dreamshader/3D_Printing/Images/blender-camera.jpg

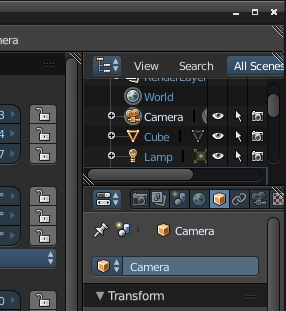
Images/blender-camera.jpg
