dreamshader/3D_Printing/Images/blender-union.jpg

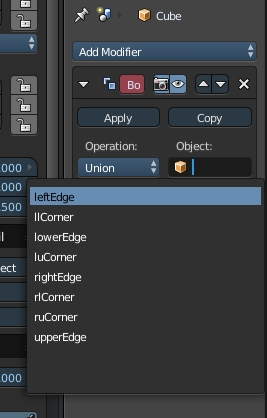
Images/blender-union.jpg
