dreamshader/3D_Printing/Images/cura-anordnung-halter.png

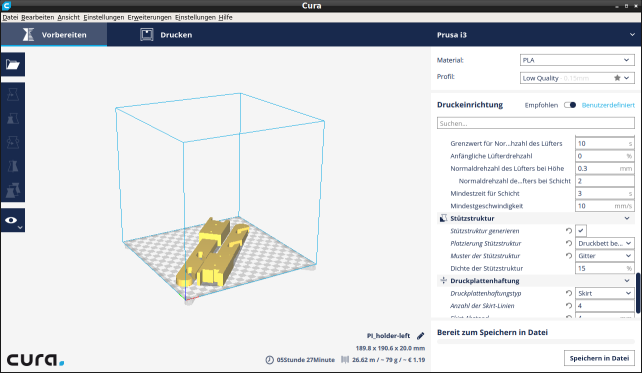
Images/cura-anordnung-halter.png
