dreamshader/3D_Printing/Images/filament-halter-teile.jpg

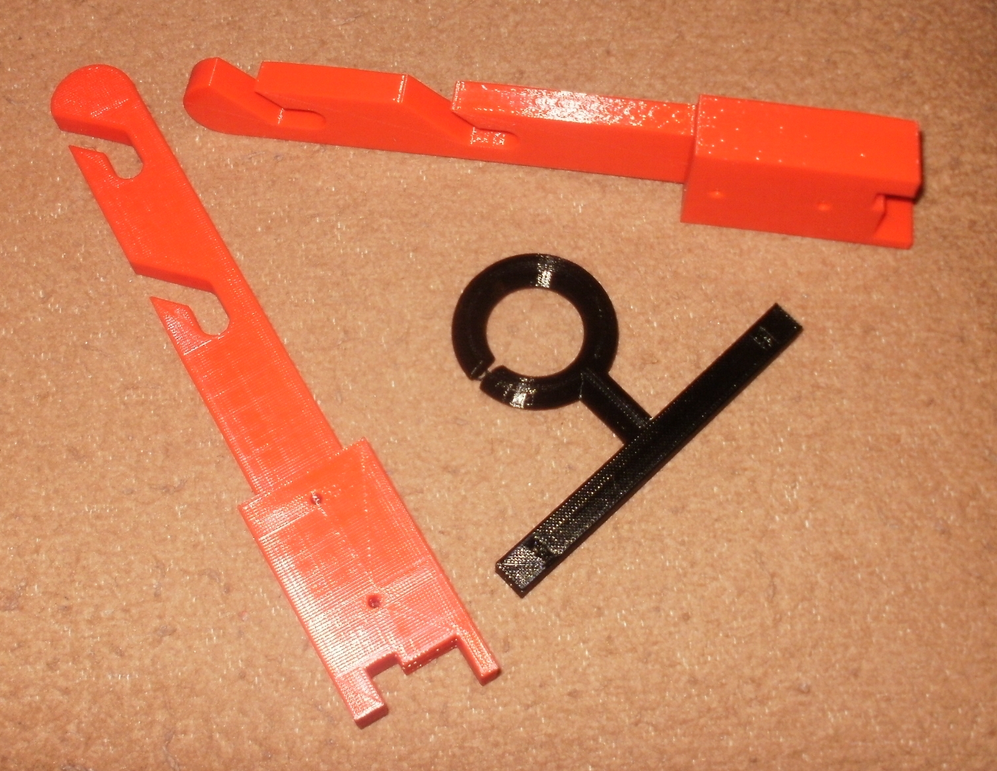
Images/filament-halter-teile.jpg
