dreamshader/3D_Printing/Images/filament-halter.jpg

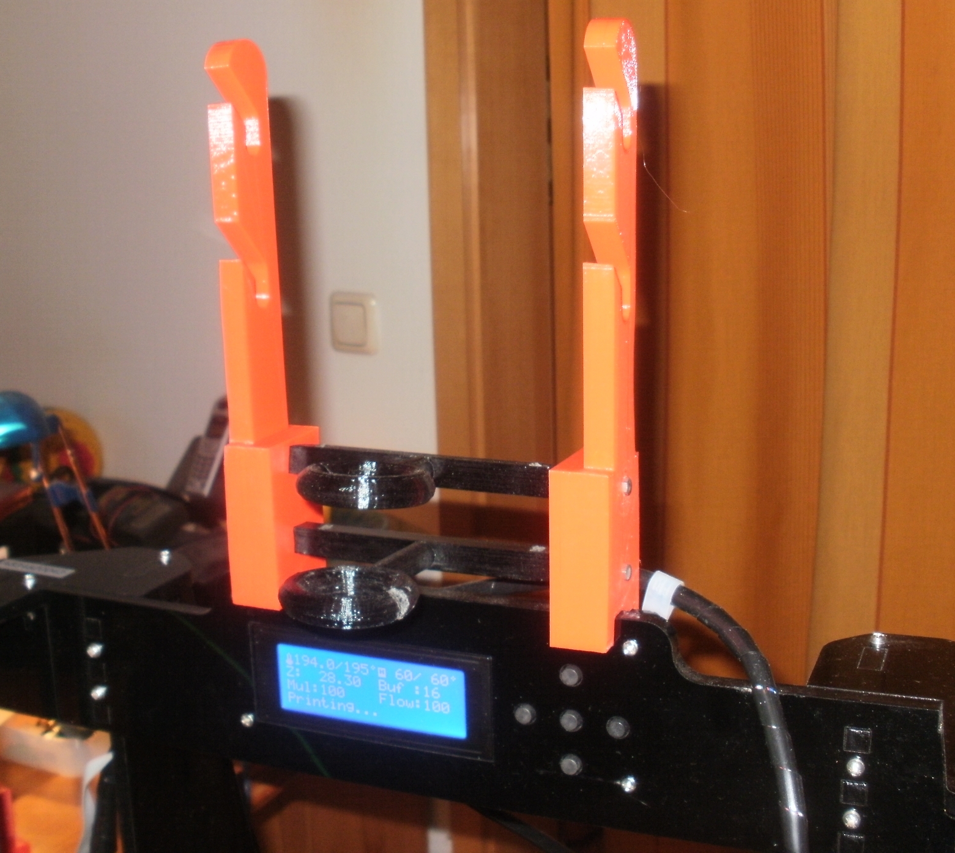
Images/filament-halter.jpg
