dreamshader/3D_Printing/Images/pi-B2-3-board.png

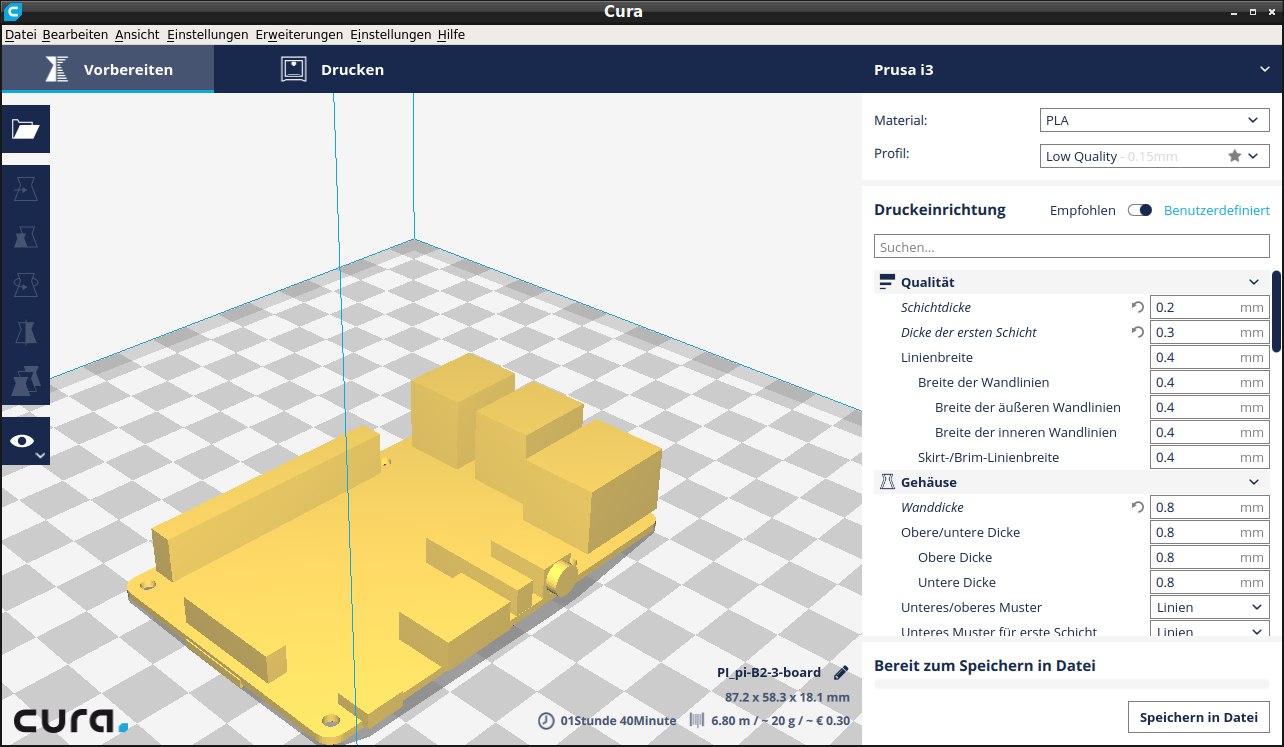
Images/pi-B2-3-board.png
