dreamshader/3D_Printing/Images/pi-bplus_2_3-2.png

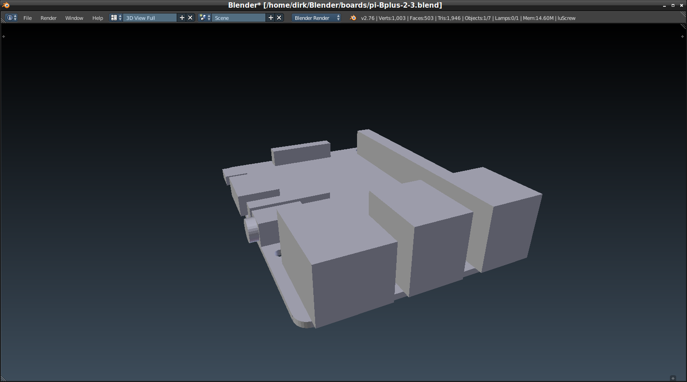
Images/pi-bplus_2_3-2.png
