dreamshader/3D_Printing/Images/pi-zero-board.png

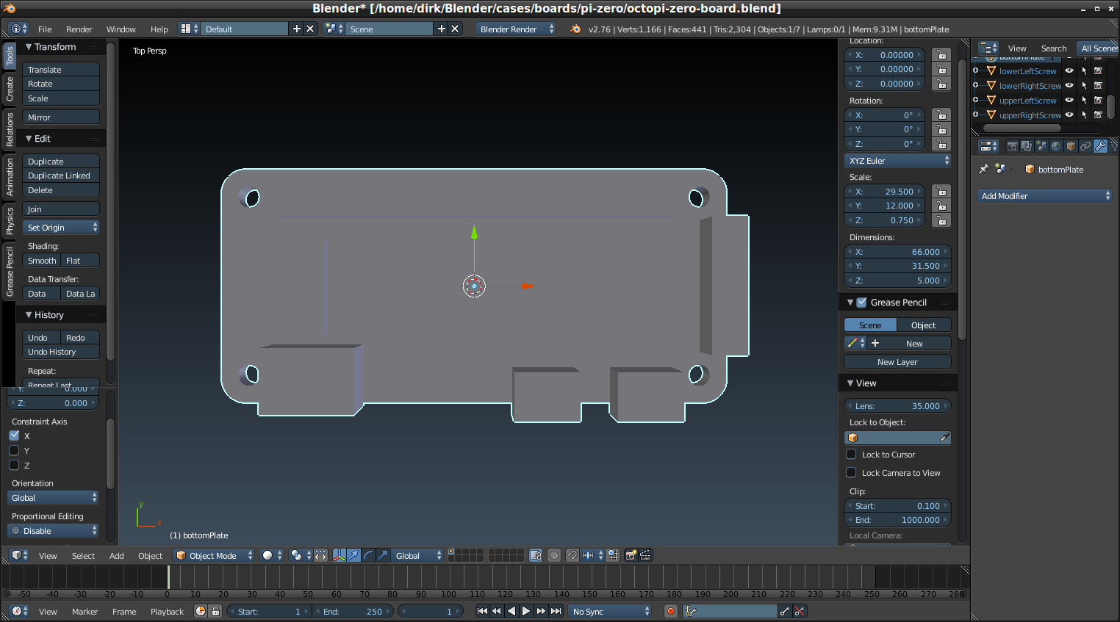
Images/pi-zero-board.png
