dreamshader/3D_Printing/Images/raw/PA100625.JPG

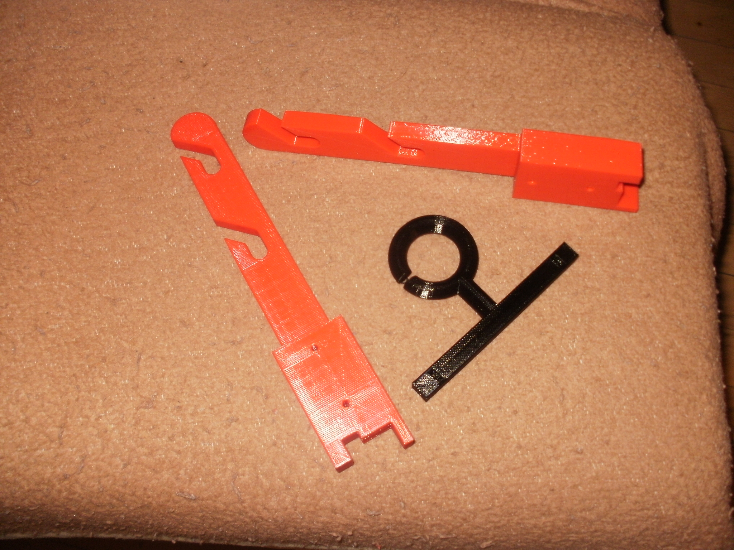
Images/raw/PA100625.JPG
