dreamshader/3D_Printing/Images/raw/PA120630.JPG

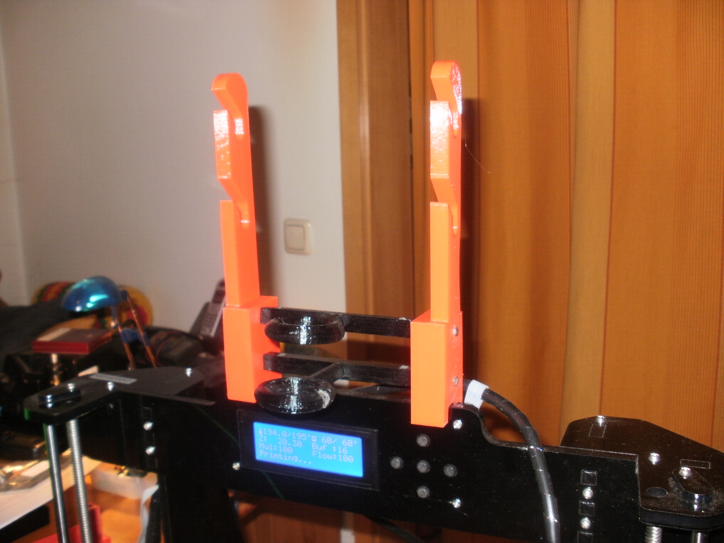
Images/raw/PA120630.JPG
