dreamshader/3D_Printing/Images/raw/PA120635.JPG

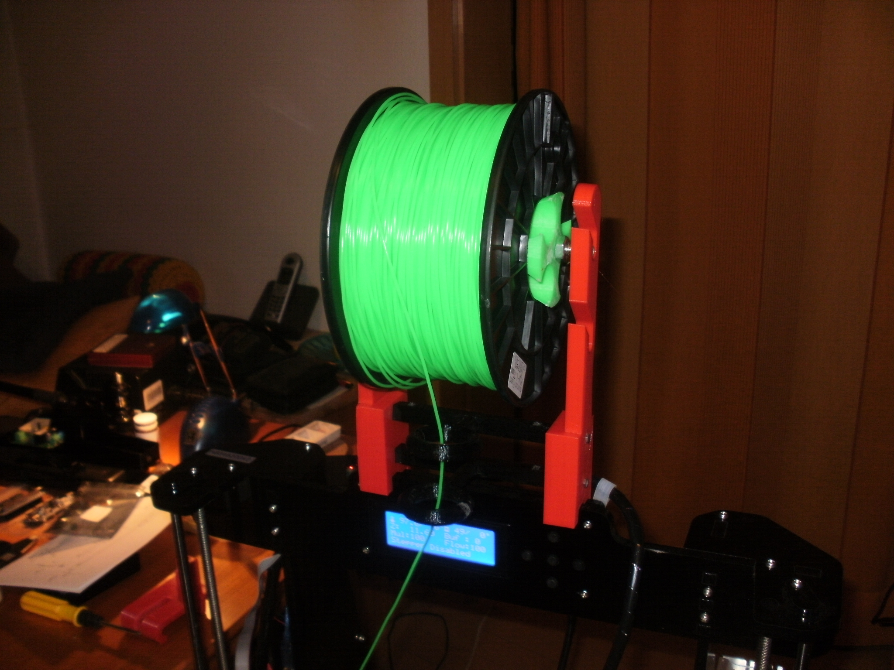
Images/raw/PA120635.JPG
