dreamshader/3D_Printing/Images/raw/PA150643.JPG

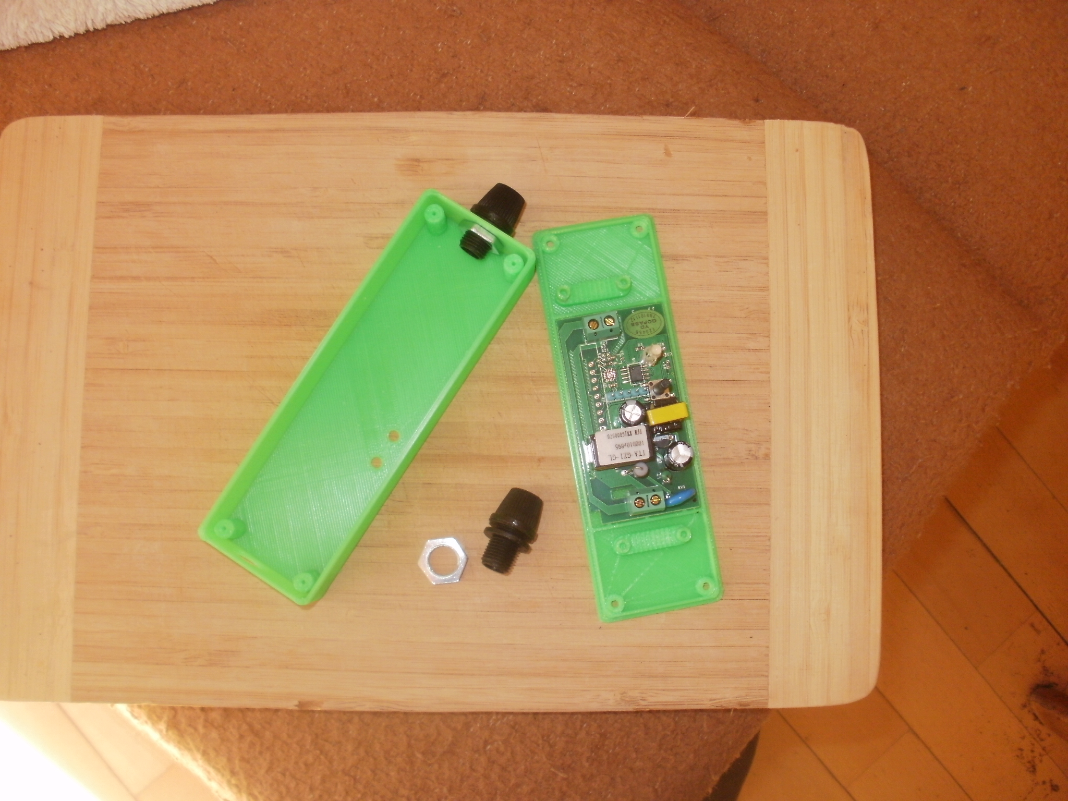
Images/raw/PA150643.JPG
