dreamshader/3D_Printing/Images/raw/PA150644.JPG

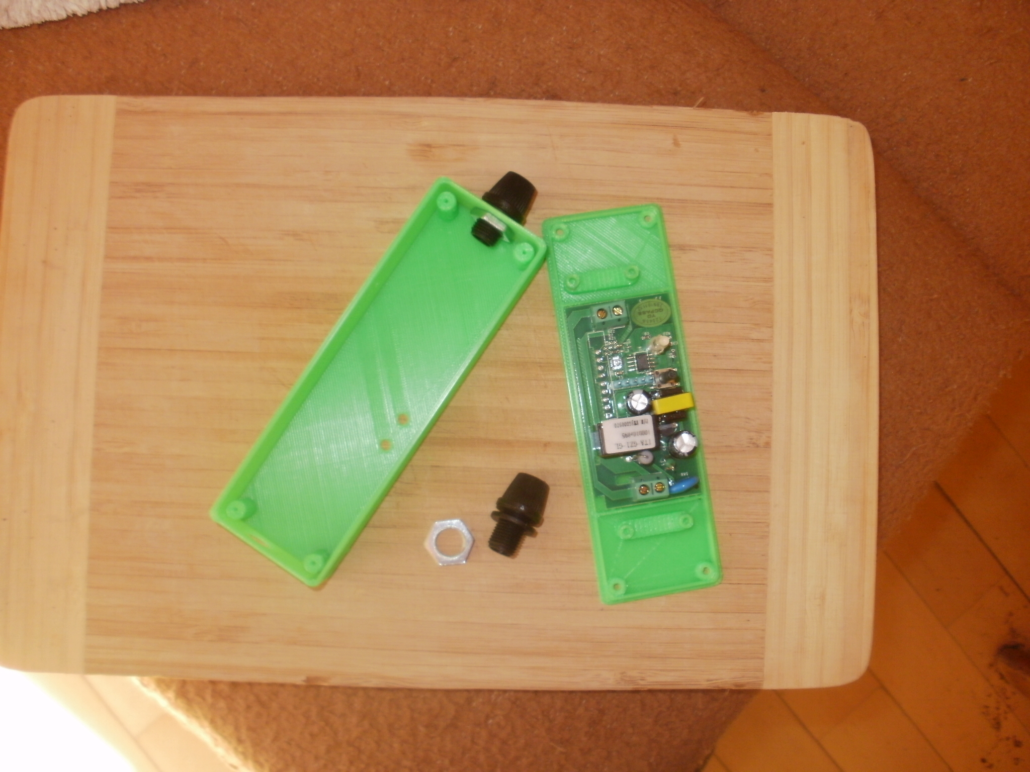
Images/raw/PA150644.JPG
