dreamshader/3D_Printing/Images/raw/PA170645.JPG

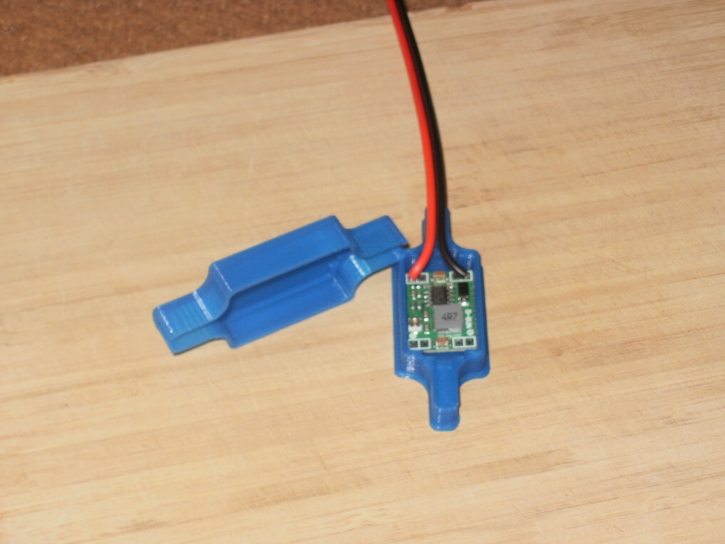
Images/raw/PA170645.JPG
