dreamshader/3D_Printing/Images/raw/PA170646.JPG

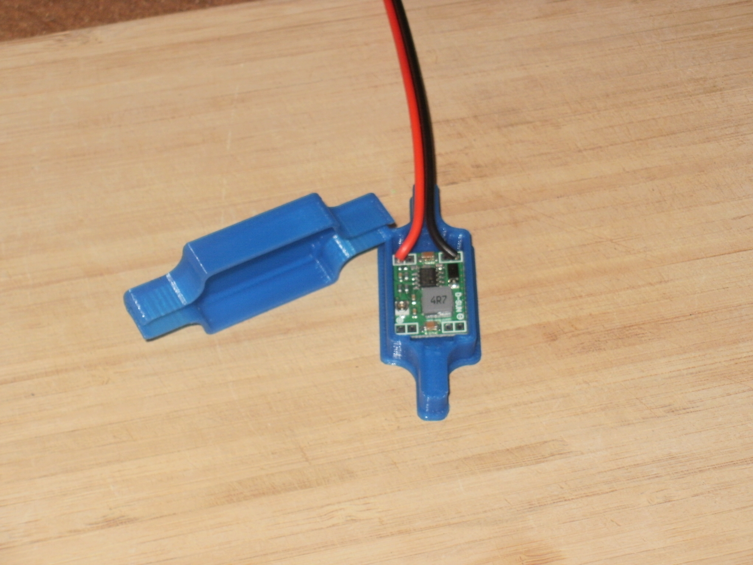
Images/raw/PA170646.JPG
