dreamshader/3D_Printing/Images/raw/PA170647.JPG

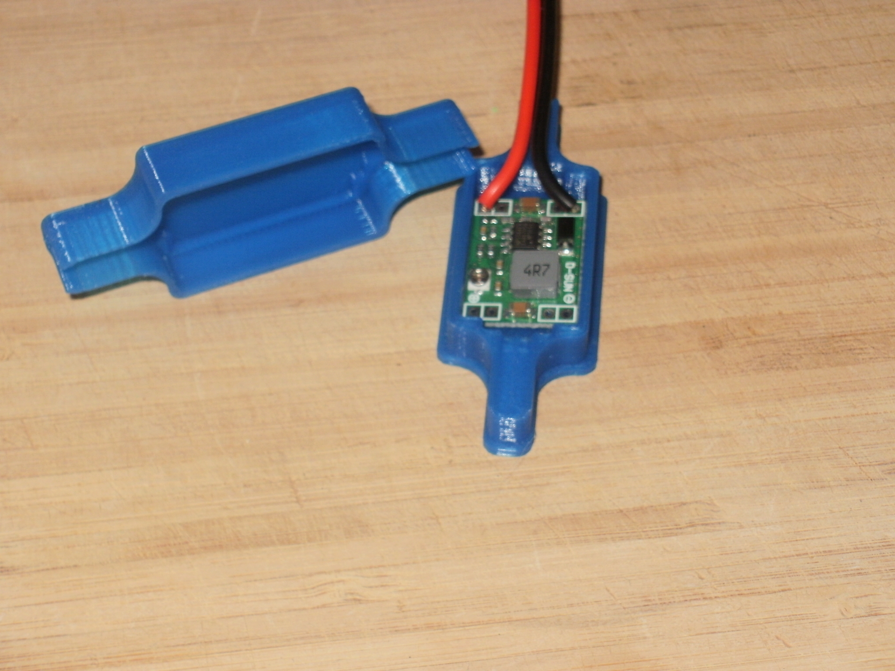
Images/raw/PA170647.JPG
