dreamshader/3D_Printing/Images/raw/PA170648.JPG

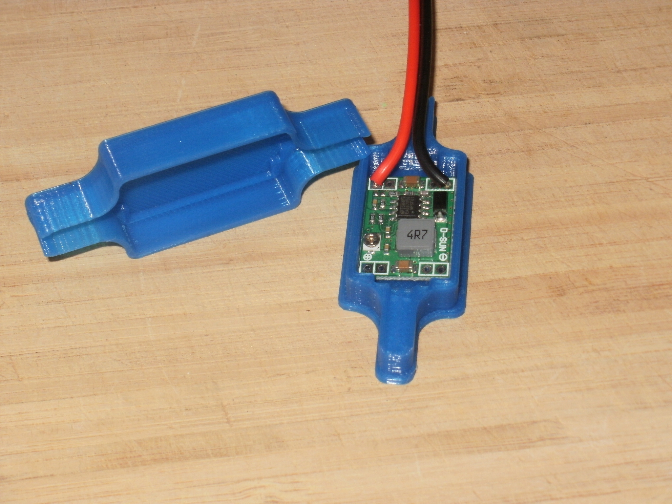
Images/raw/PA170648.JPG
