dreamshader/3D_Printing/Images/raw/PC060654.JPG

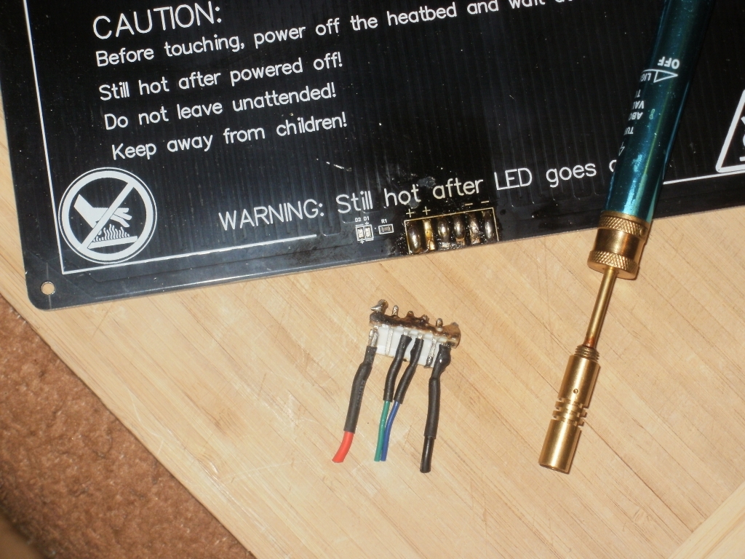
Images/raw/PC060654.JPG
