dreamshader/3D_Printing/Images/raw/PC060656.JPG

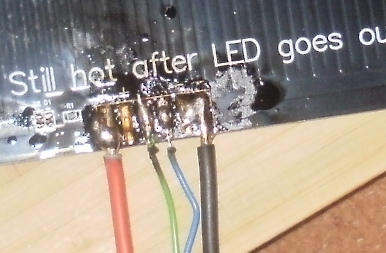
Images/raw/PC060656.JPG
