dreamshader/3D_Printing/Images/raw/PC060659.JPG

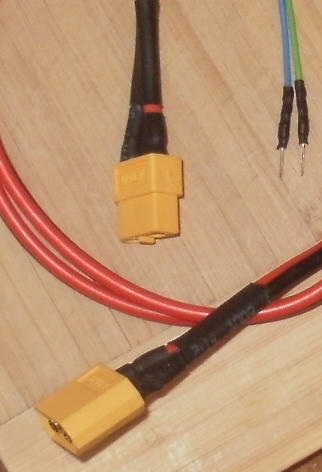
Images/raw/PC060659.JPG
