dreamshader/3D_Printing/Images/raw/PC060662.JPG

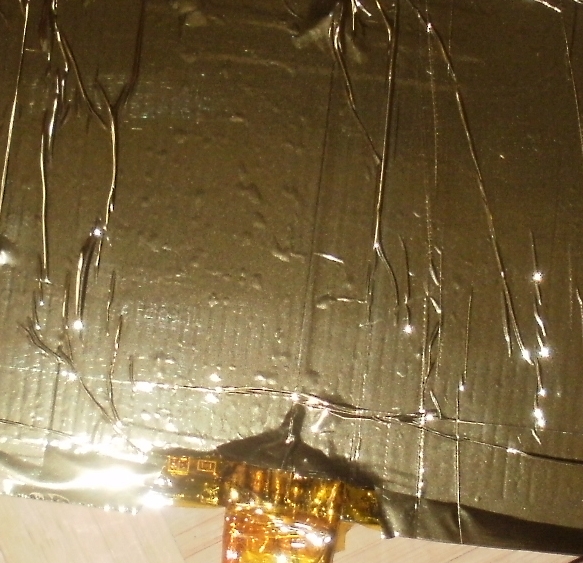
Images/raw/PC060662.JPG
