dreamshader/3D_Printing/Images/raw/PC060664.JPG

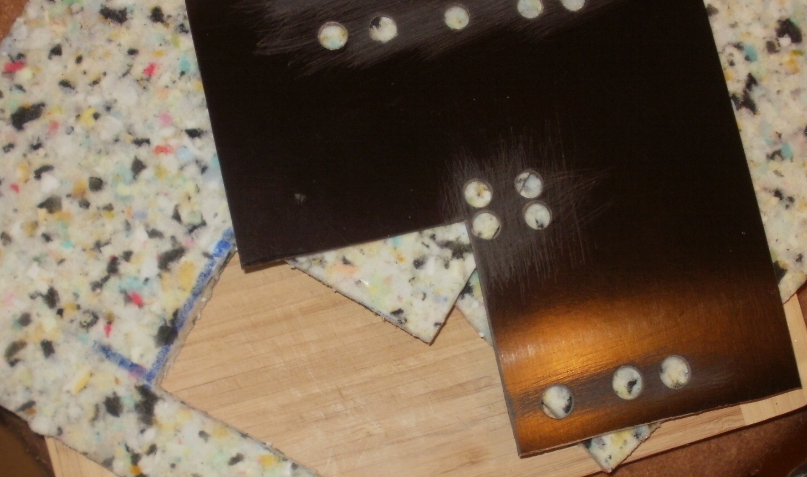
Images/raw/PC060664.JPG
