dreamshader/3D_Printing/Images/raw/PC070672.JPG

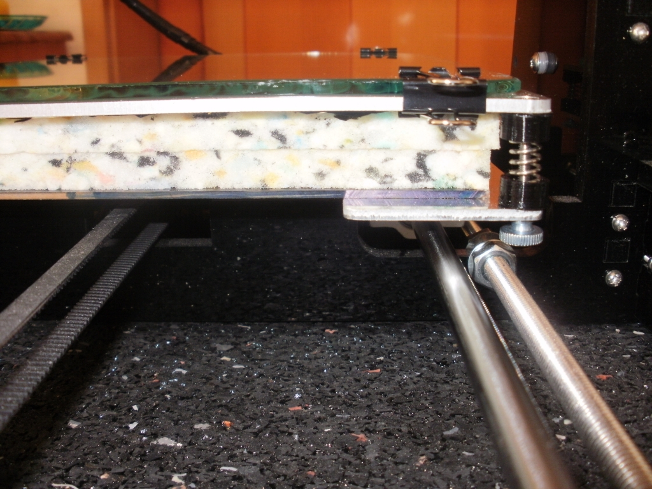
Images/raw/PC070672.JPG
