dreamshader/3D_Printing/Images/raw/PC070674.JPG

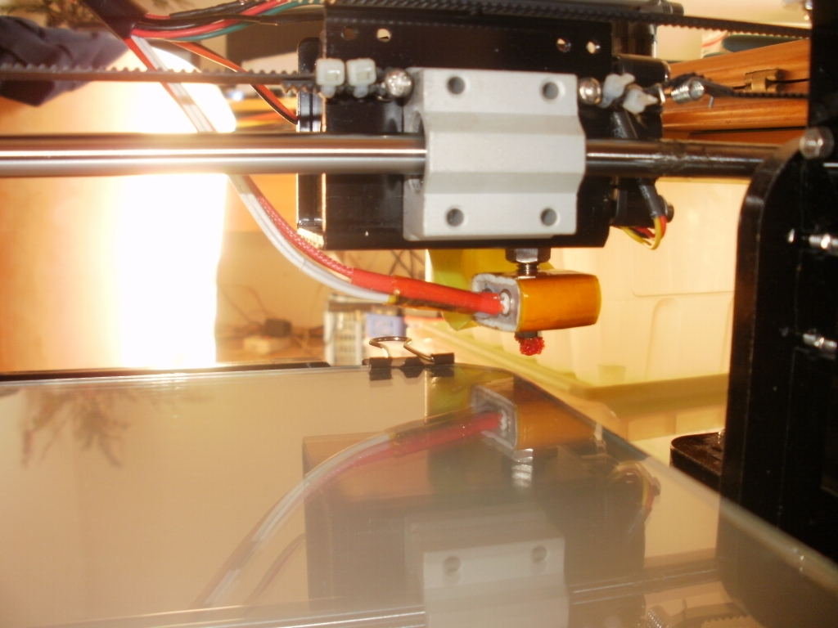
Images/raw/PC070674.JPG
