dreamshader/3D_Printing/Images/raw/PC070677.JPG

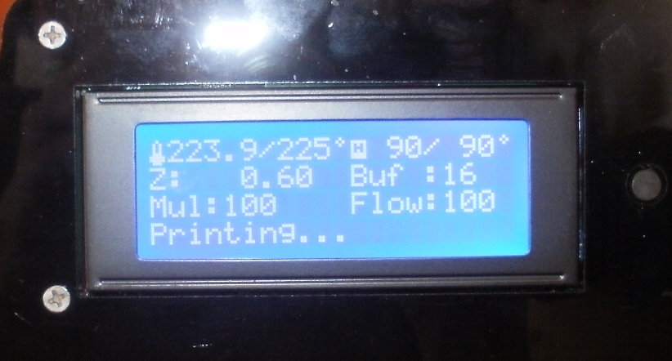
Images/raw/PC070677.JPG
