dreamshader/3D_Printing/Images/raw/sonoff-case-2.jpg

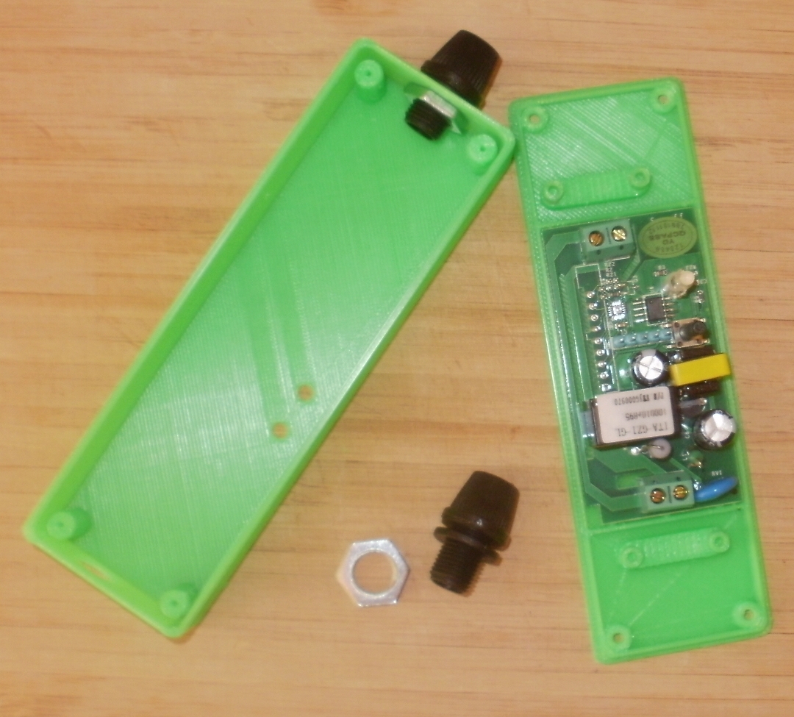
Images/raw/sonoff-case-2.jpg
