dreamshader/3D_Printing/Images/Rollen_Reduzierung.jpg

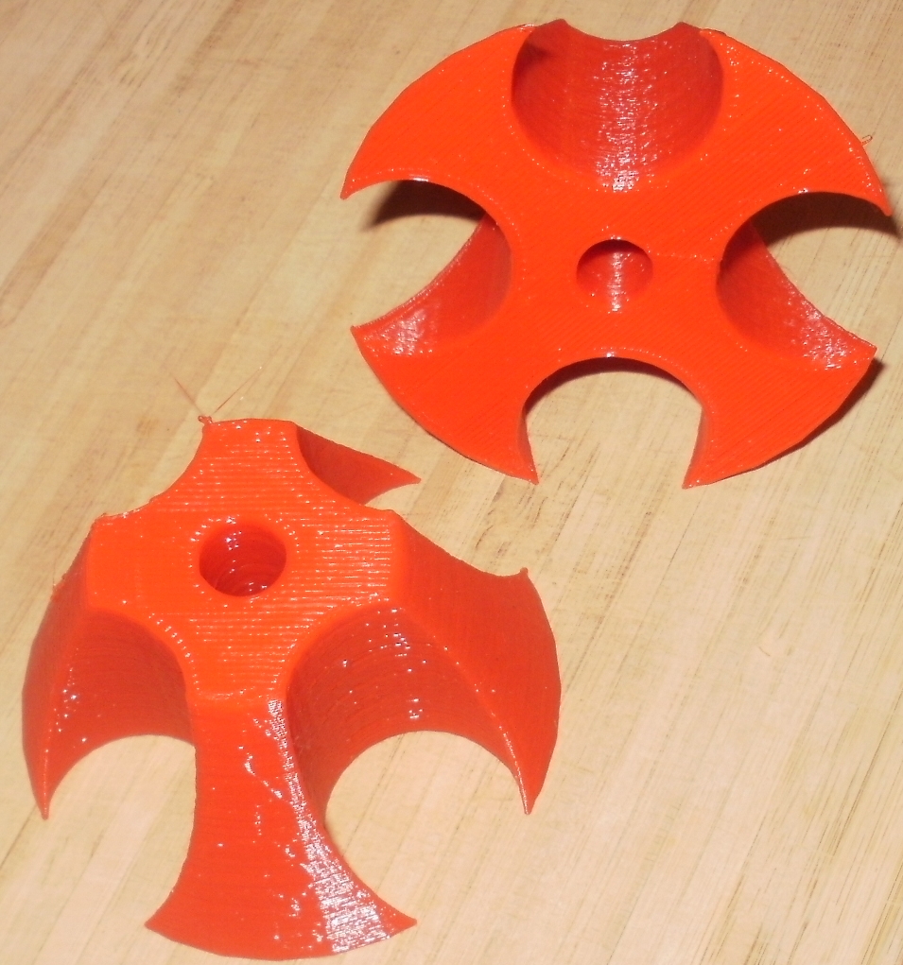
Images/Rollen_Reduzierung.jpg
