dreamshader/3D_Printing/Images/sonoff-screenshot-1.png

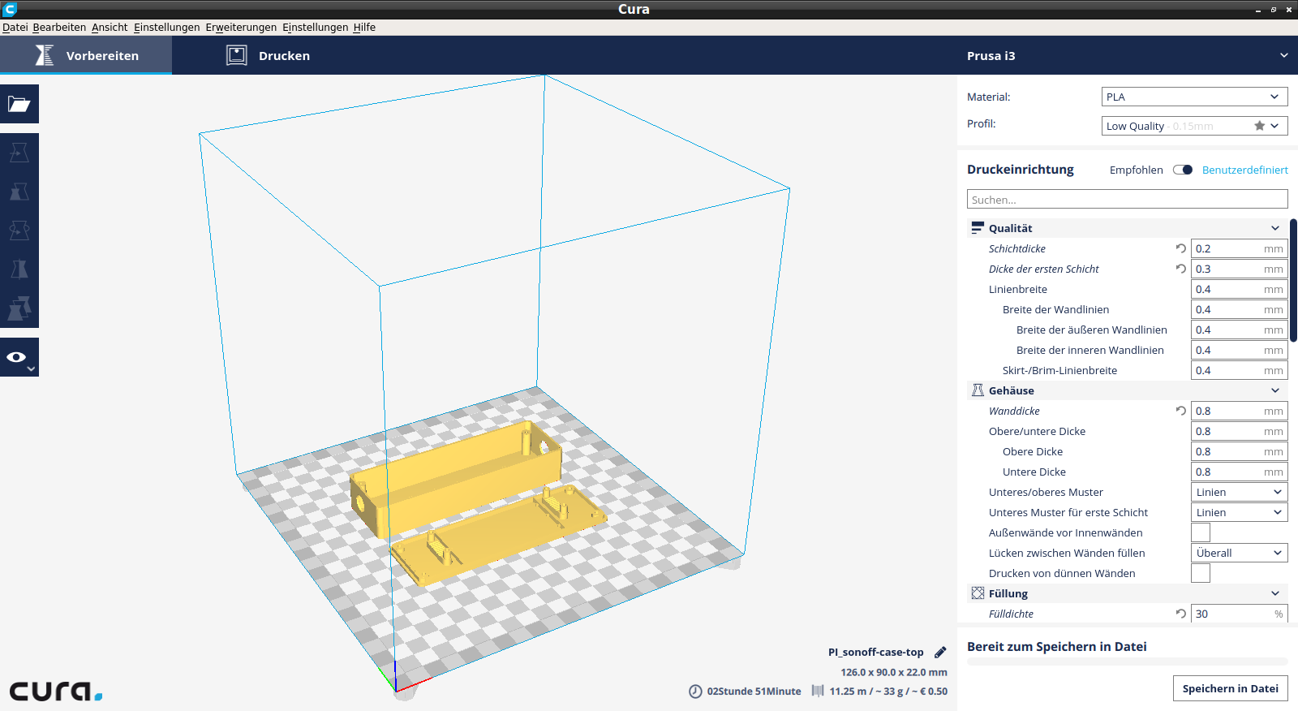
Images/sonoff-screenshot-1.png
