dreamshader/3D_Printing/Images/sonoff-screenshot-2.png

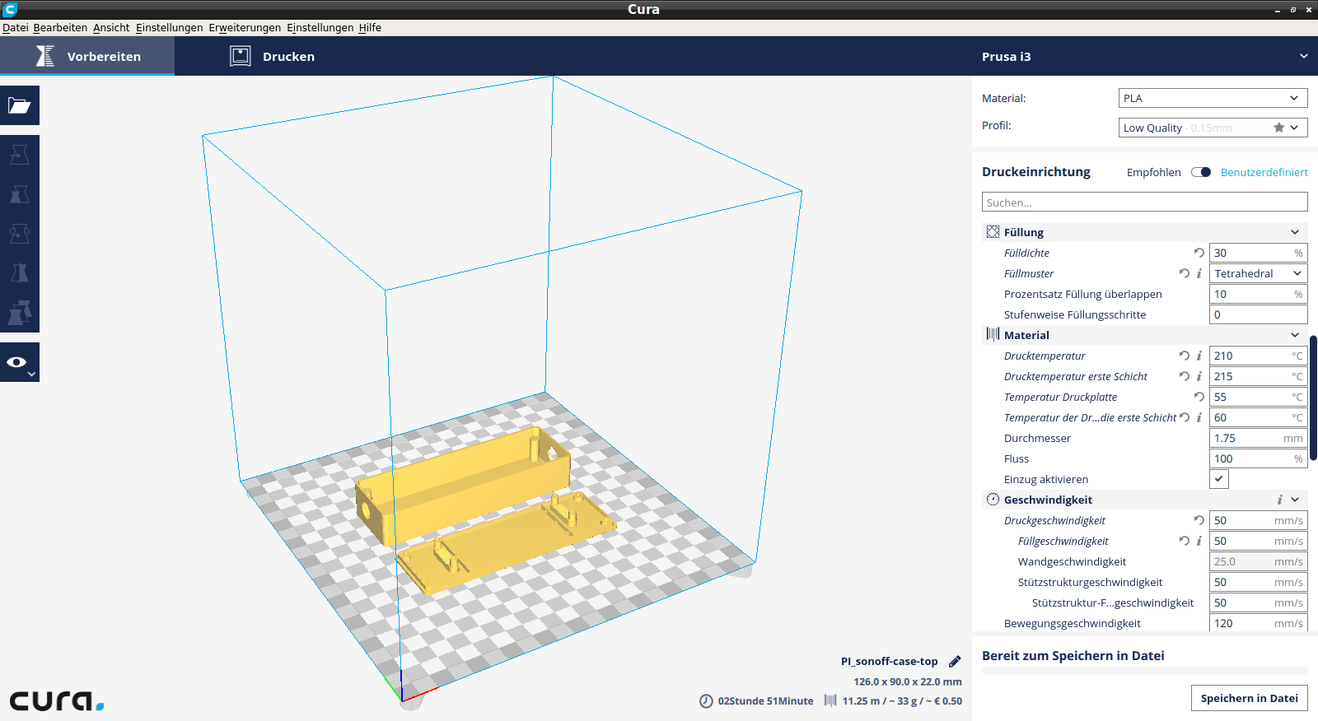
Images/sonoff-screenshot-2.png
