dreamshader/3D_Printing/Images/sonoff-screenshot-3.png

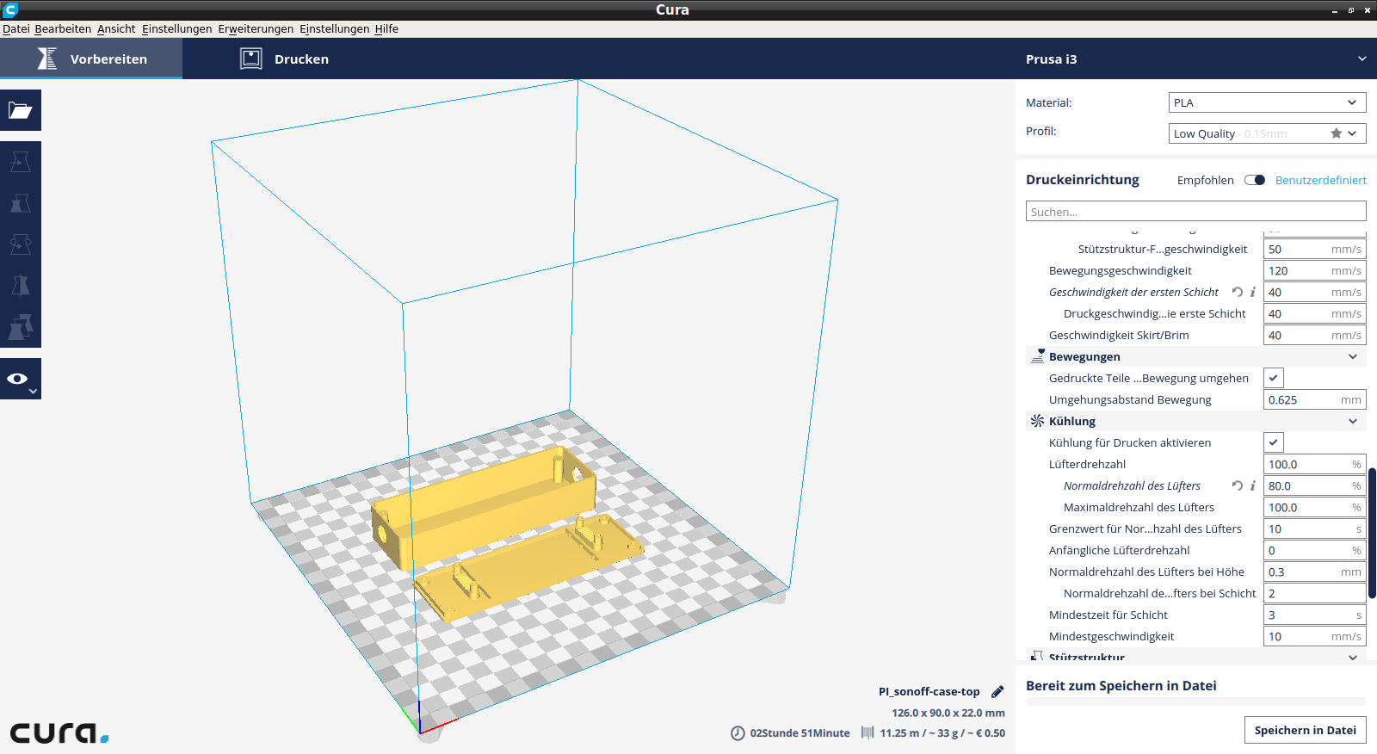
Images/sonoff-screenshot-3.png
