dreamshader/3D_Printing/Images/sonoff-screenshot-4.png

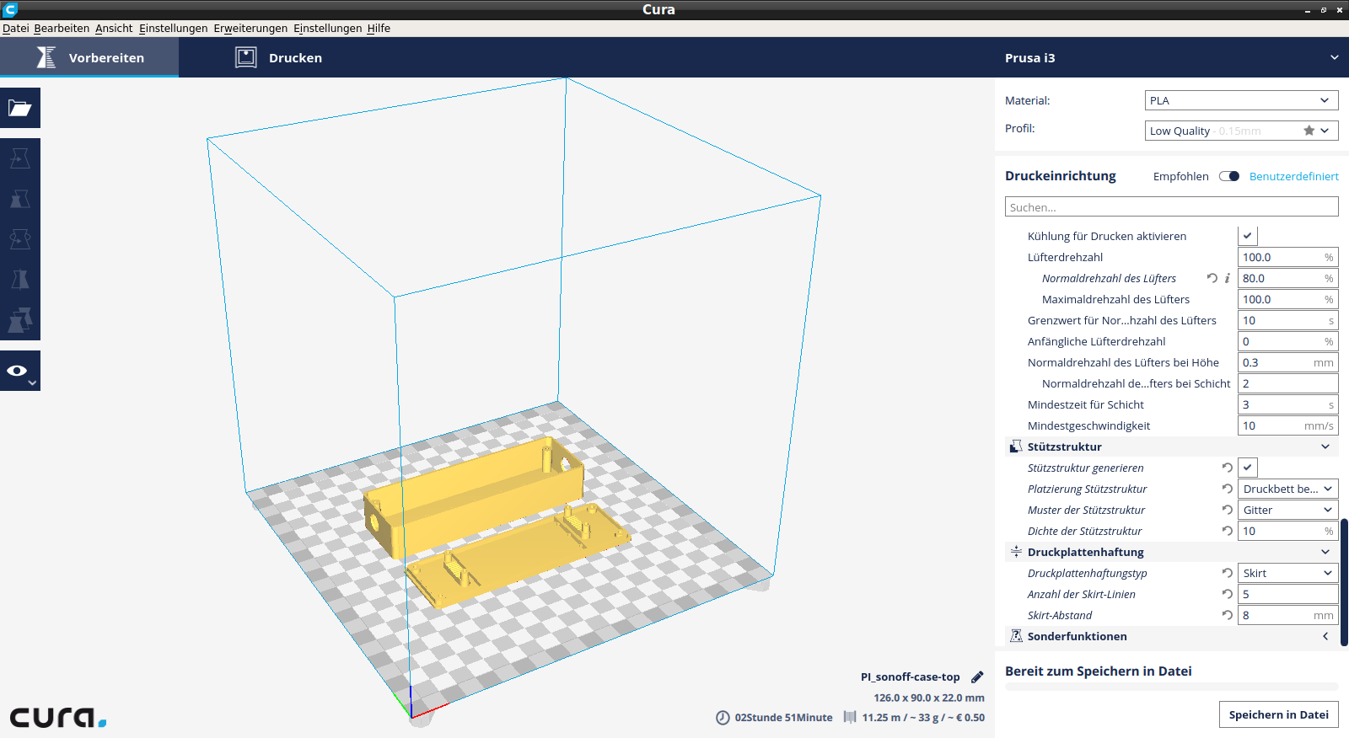
Images/sonoff-screenshot-4.png
