dreamshader/3D_Printing/Images/stepdown-case.jpg

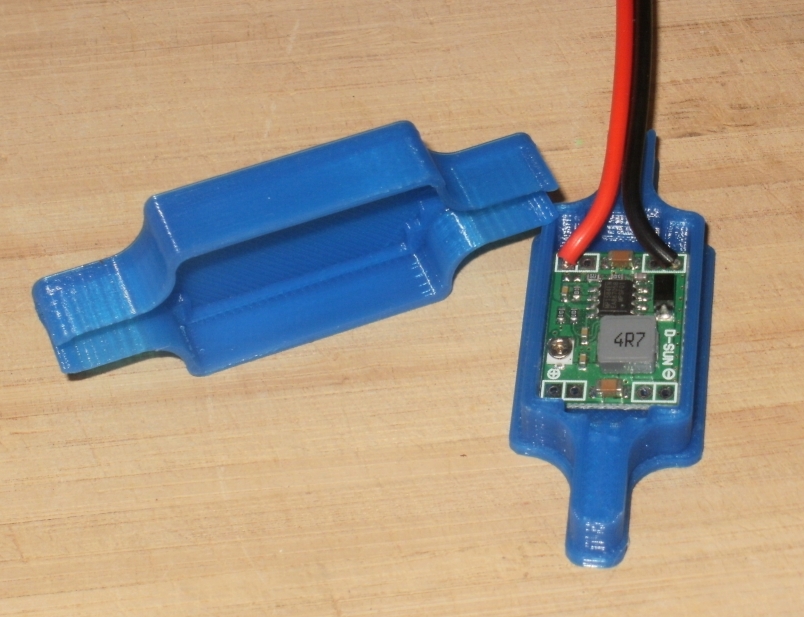
Images/stepdown-case.jpg
